t-dsp/t-dsp_core/3d_models/COMBO_XLR_NCJ6FI-H-0.stp

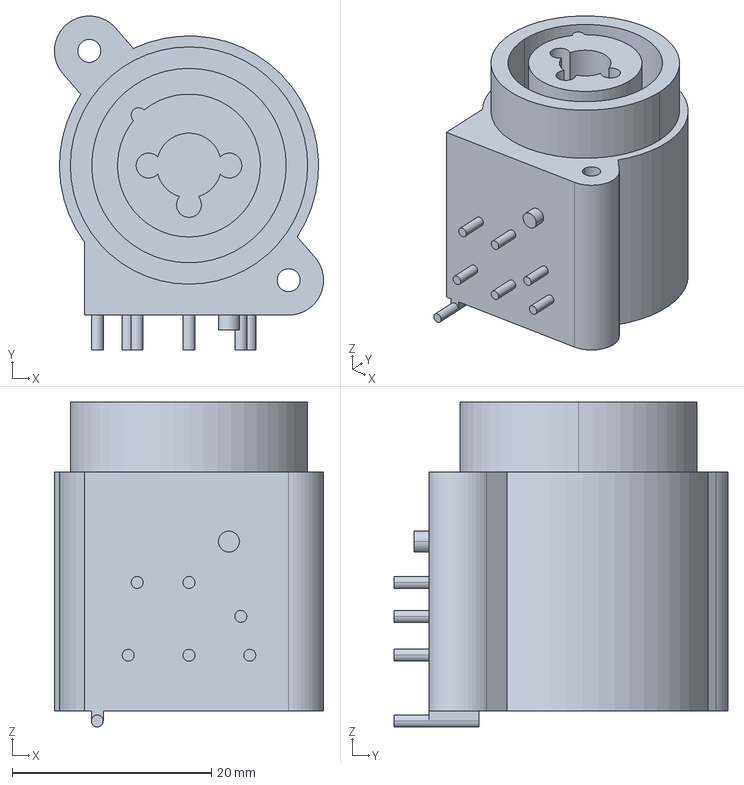
[picture p20: CAD file, 2026-02-28]
3d_models/COMBO_XLR_NCJ6FI-H-0.stp
27.0 x 33.5 x 32.6 mm
