t-dsp/t-dsp_core/3d_models/PRT-14417.step

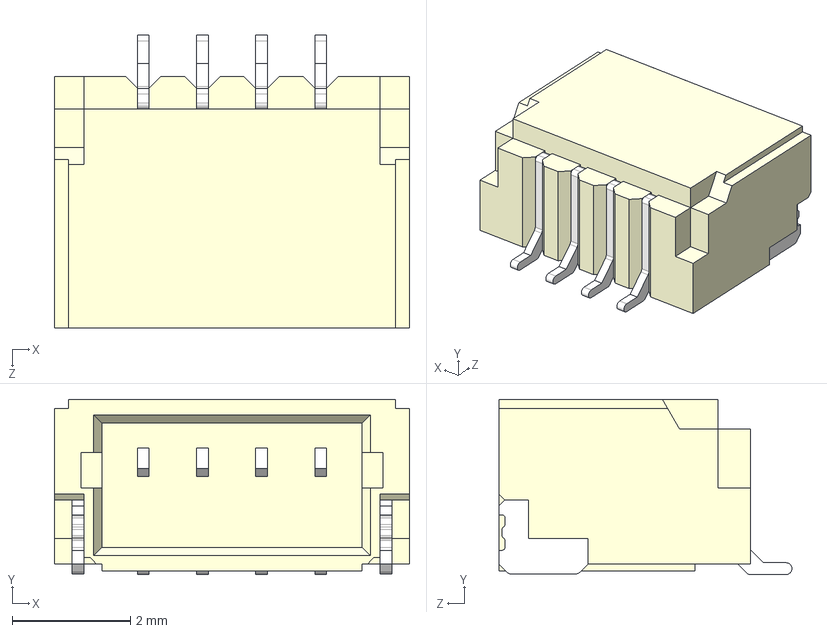
[picture p21: CAD file, 2026-02-28]
3d_models/PRT-14417.step
6.00 x 2.96 x 4.95 mm
