t-dsp/t-dsp_core/3d_models/COMBO-NCJ6FA-H.step

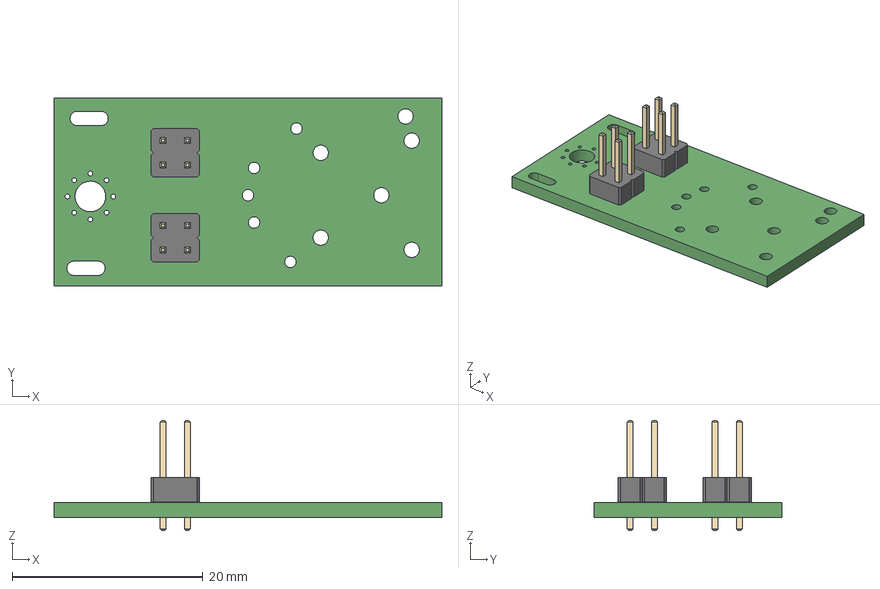
[picture p22: CAD file, 2026-02-28]
3d_models/COMBO-NCJ6FA-H.step
40.6 x 19.7 x 11.5 mm
