t-dsp/t-dsp_core/3d_models/35RAPC7JS_SIMPLIFIED.step

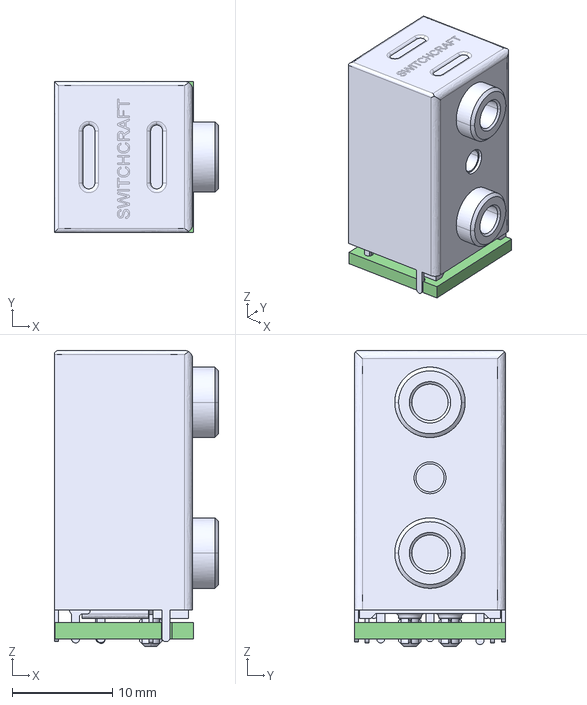
[picture p24: CAD file, 2026-02-28]
3d_models/35RAPC7JS_SIMPLIFIED.step
16.4 x 15.0 x 29.5 mm
IO_3.5_35RAPC7JS PCB
