t-dsp/t-dsp_core/3d_models/TFT_320x240_touch_r0.step

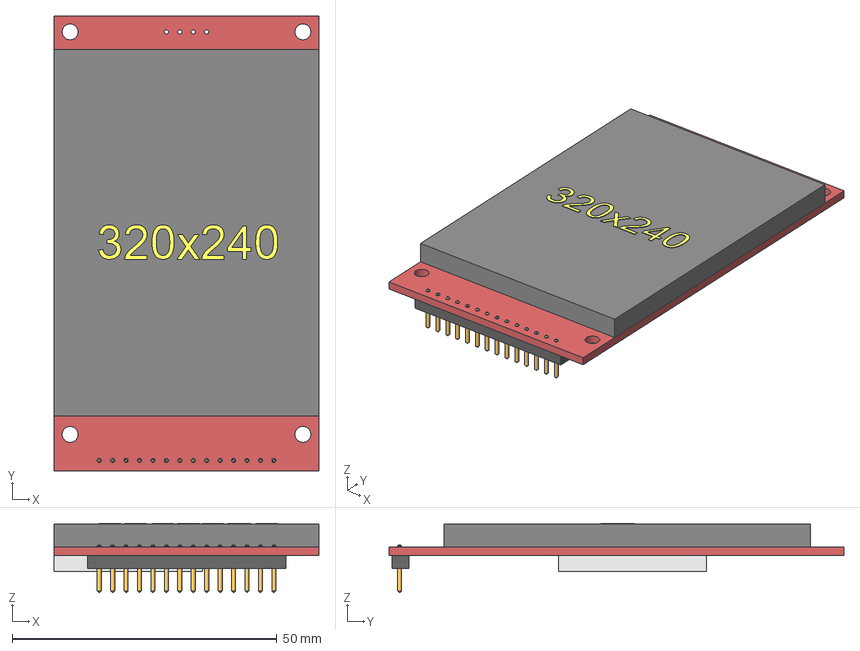
[picture p25: CAD file, 2026-02-28]
3d_models/TFT_320x240_touch_r0.step
50.0 x 86.0 x 13.1 mm
Body-header
Body-pins
Body-display
Body-sdcard
Body-board
