t-dsp/t-dsp_core/3d_models/pjras1x2s_Series.STEP

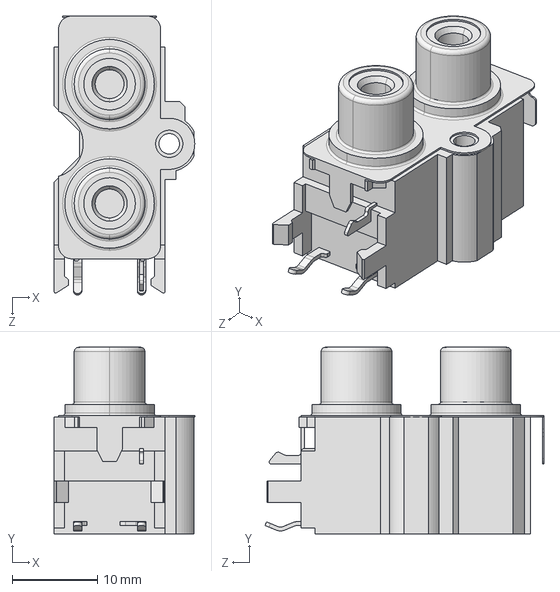
[picture p26: CAD file, 2026-02-28]
3d_models/pjras1x2s_Series.STEP
16.5 x 21.9 x 32.7 mm
