t-dsp/t-dsp_core/3d_models/MF-LSMF300_24X-2.stp

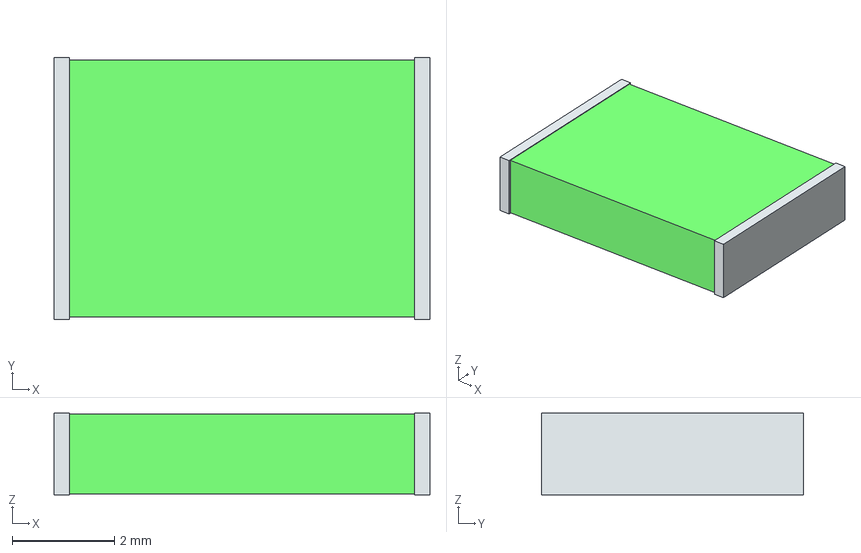
[picture p28: CAD file, 2026-02-28]
3d_models/MF-LSMF300_24X-2.stp
7.36 x 5.12 x 1.60 mm
term1
term2
