t-dsp/t-dsp_core/3d_models/EN11-HSM1AF15.STEP

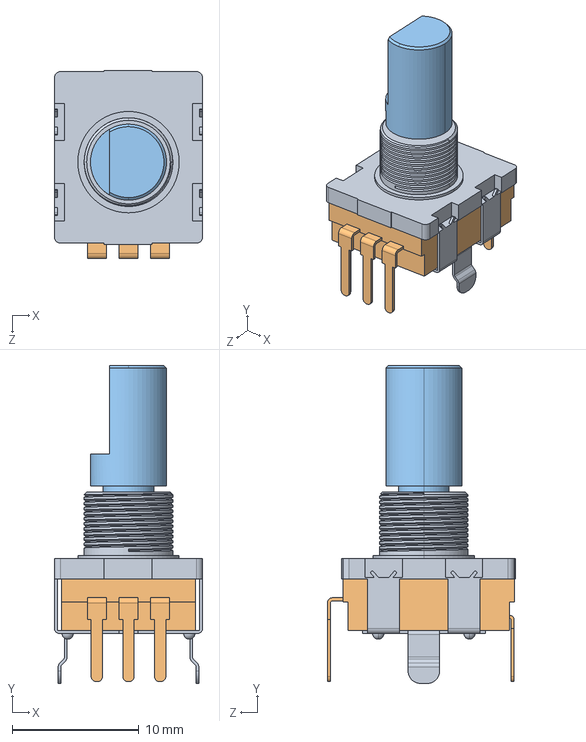
[picture p29: CAD file, 2026-02-28]
3d_models/EN11-HSM1AF15.STEP
11.7 x 25.1 x 14.9 mm
