t-dsp/t-dsp_core/3d_models/SD_CARD_DM3D-SF.step

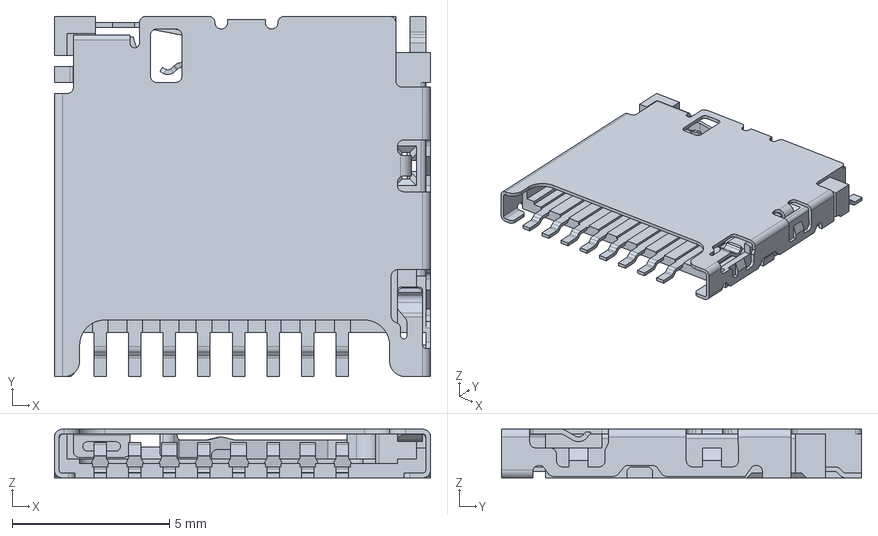
[picture p30: CAD file, 2026-02-28]
3d_models/SD_CARD_DM3D-SF.step
11.9 x 11.4 x 1.55 mm
