t-dsp/t-dsp_core/3d_models/SK6812.step

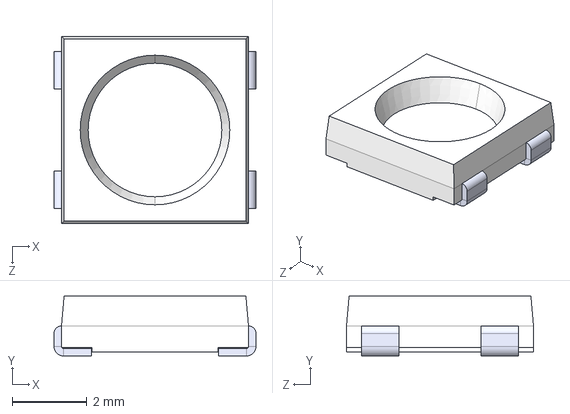
[picture p31: CAD file, 2026-02-28]
3d_models/SK6812.step
5.40 x 1.60 x 5.00 mm
