t-dsp/t-dsp_core/3d_models/c-292304-1-b-3d.stp

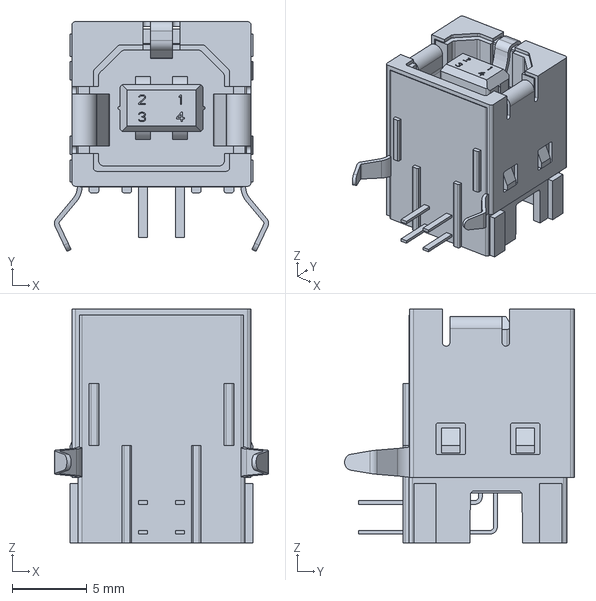
[picture p32: CAD file, 2026-02-28]
3d_models/c-292304-1-b-3d.stp
14.4 x 15.4 x 15.7 mm
