t-dsp/t-dsp_core/3d_models/PinHeader_2x02_P2.54mm_Vertical.step

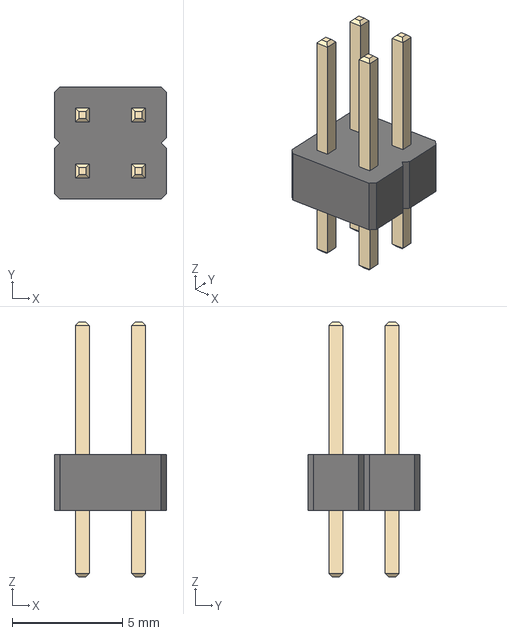
[picture p33: CAD file, 2026-02-28]
3d_models/PinHeader_2x02_P2.54mm_Vertical.step
5.08 x 5.08 x 11.5 mm
