t-dsp/t-dsp_core/3d_models/T10W--3DModel-STEP-56544.STEP

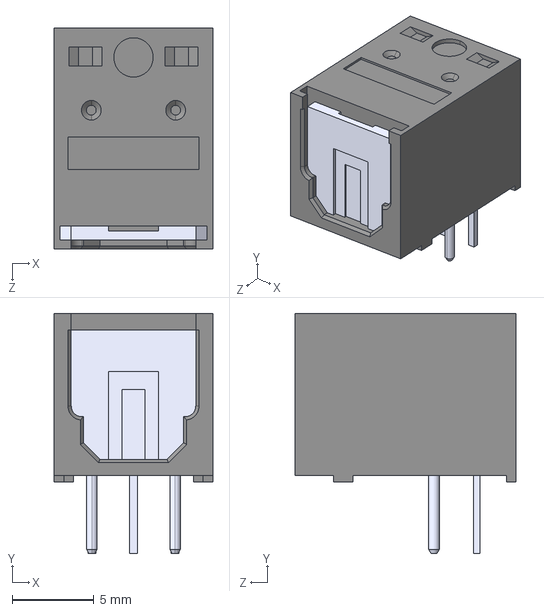
[picture p34: CAD file, 2026-02-28]
3d_models/T10W--3DModel-STEP-56544.STEP
9.70 x 14.7 x 13.5 mm
