t-dsp/t-dsp_core/3d_models/DIN-5.STEP

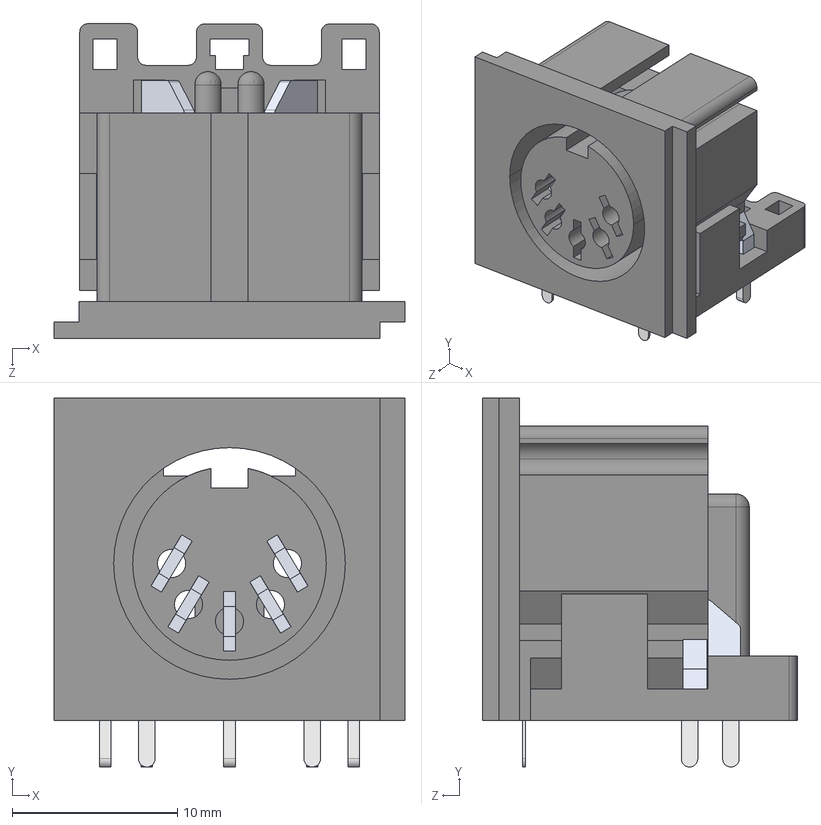
[picture p35: CAD file, 2026-02-28]
3d_models/DIN-5.STEP
21.2 x 22.3 x 19.0 mm
DIN5 A
DIN5 B
DIN5 C
DIN D x 2
DIN E x 2
DIN EE x 2
DIN G
DIN DD x 2
