t-dsp/t-dsp_core/3d_models/TOSLINK_3D_MODEL_PLT133_T9.step

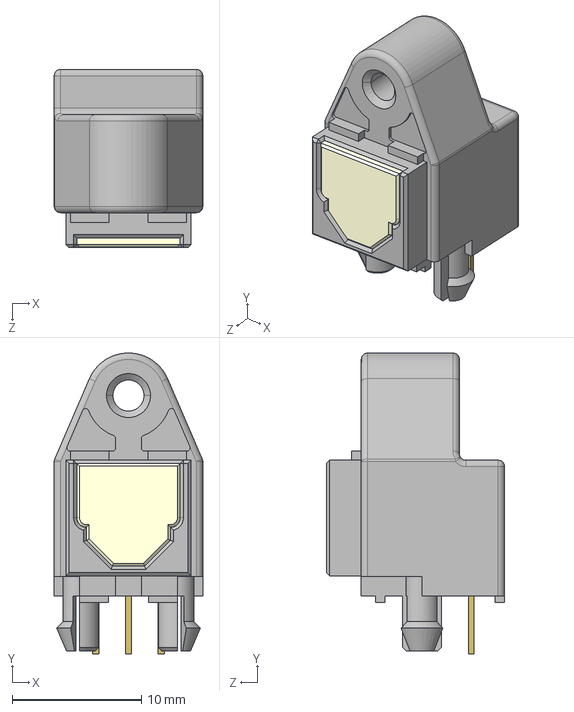
[picture p36: CAD file, 2026-02-28]
3d_models/TOSLINK_3D_MODEL_PLT133_T9.step
11.5 x 23.3 x 13.8 mm
