t-dsp/t-dsp_core/3d_models/Same_Sky_SJ3-35083D-TR.step

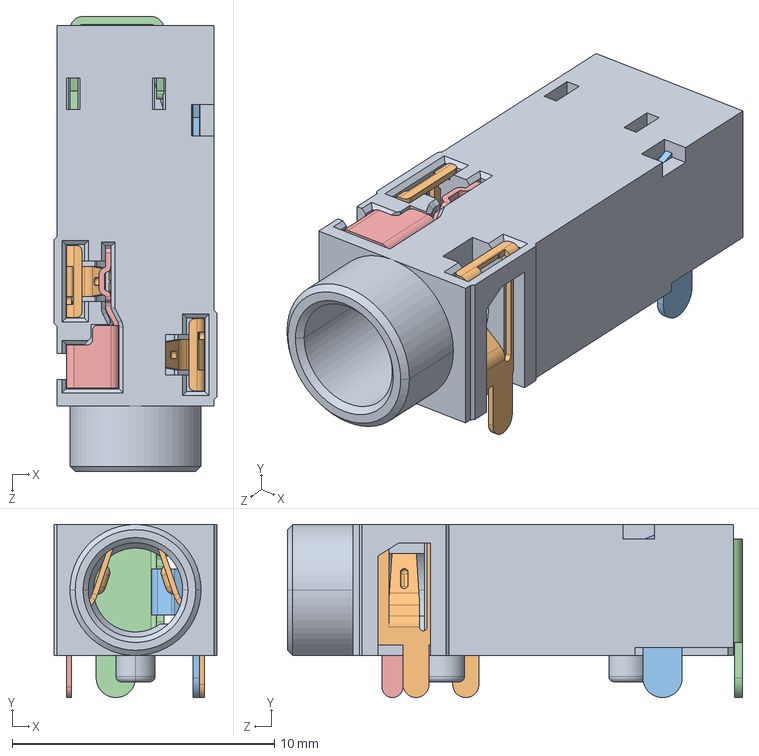
[picture p37: CAD file, 2026-02-28]
3d_models/Same_Sky_SJ3-35083D-TR.step
6.20 x 6.60 x 17.3 mm
