t-dsp/t-dsp_core/3d_models/2120--3DModel-STEP-630548.STEP

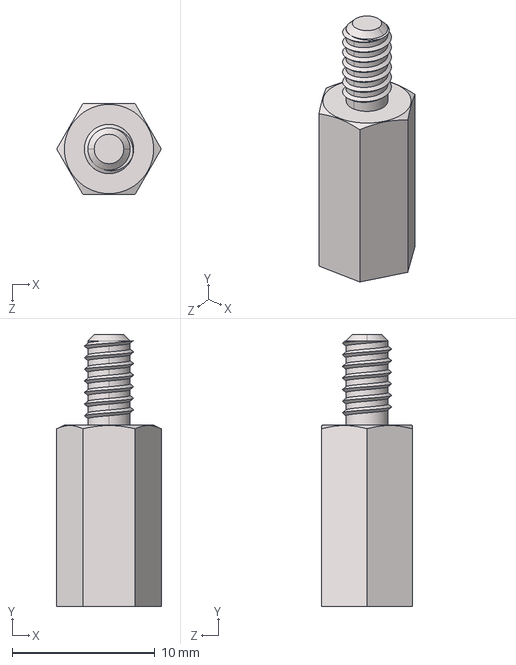
[picture p38: CAD file, 2026-02-28]
3d_models/2120--3DModel-STEP-630548.STEP
7.33 x 19.1 x 6.35 mm
