t-dsp/t-dsp_core/3d_models/3.5MM_STEREO_35RAPC4BHN2.STEP

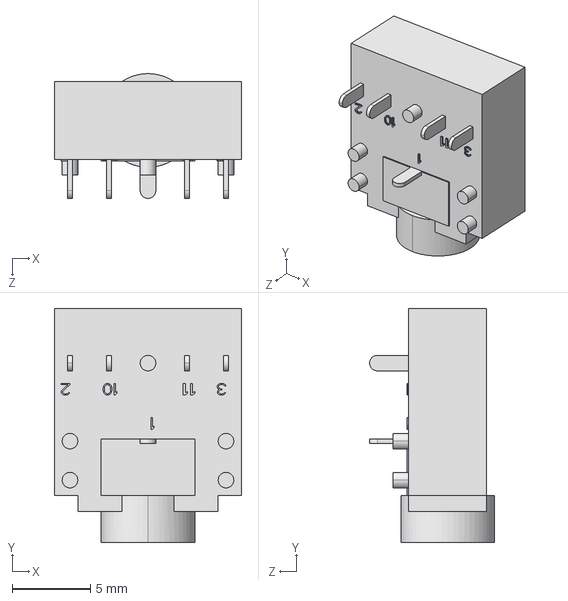
[picture p39: CAD file, 2026-02-28]
3d_models/3.5MM_STEREO_35RAPC4BHN2.STEP
12.0 x 15.0 x 8.00 mm
