t-dsp/t-dsp_core/3d_models/SPDIF_pjran1x1_Series.STEP

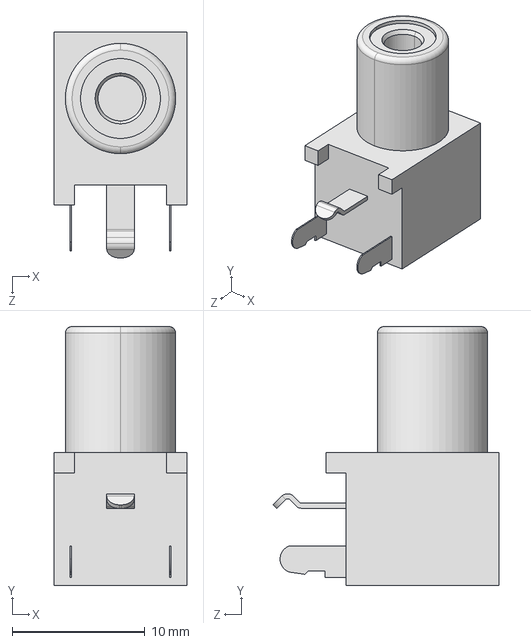
[picture p40: CAD file, 2026-02-28]
3d_models/SPDIF_pjran1x1_Series.STEP
10.00 x 19.5 x 17.0 mm
