t-dsp/t-dsp_core/3d_models/LED_SK6812MINI-E.step

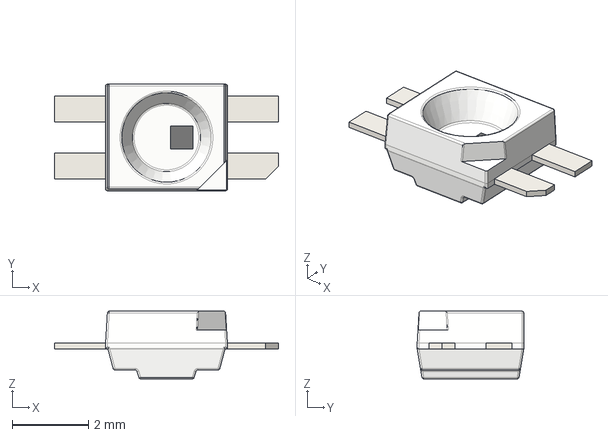
[picture p41: CAD file, 2026-02-28]
3d_models/LED_SK6812MINI-E.step
5.88 x 2.80 x 1.78 mm
