t-dsp/t-dsp_core/3d_models/USB-B1HS - USB-B1H Interconnect USB Type B.stp

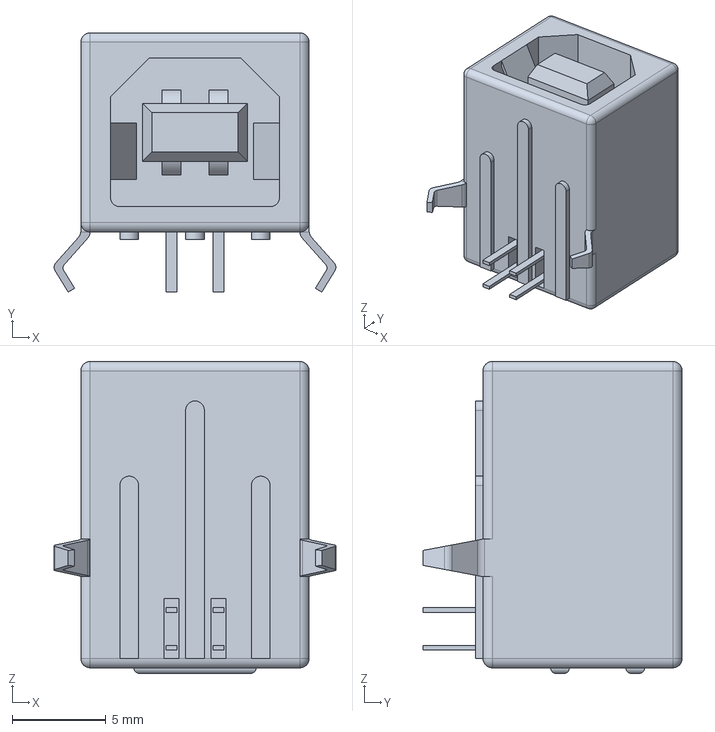
[picture p42: CAD file, 2026-02-28]
3d_models/USB-B1HS - USB-B1H Interconnect USB Type B.stp
15.0 x 13.8 x 16.6 mm
