t-dsp/t-dsp_core/3d_models/CP_Radial_D10.0mm_P5.00mm.step

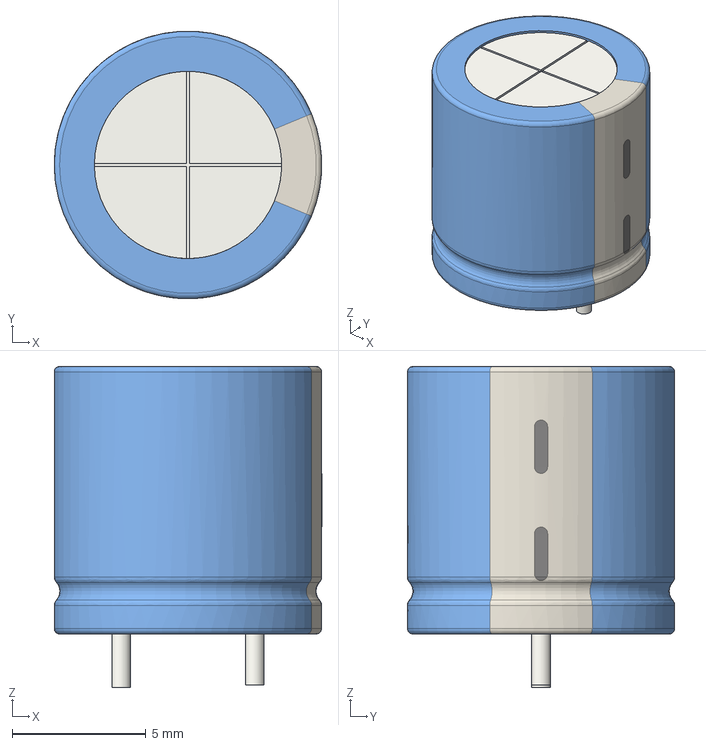
[picture p43: CAD file, 2026-02-28]
3d_models/CP_Radial_D10.0mm_P5.00mm.step
10.00 x 9.99 x 12.0 mm
