t-dsp/t-dsp_core/3d_models/DMG2307L-7.stp

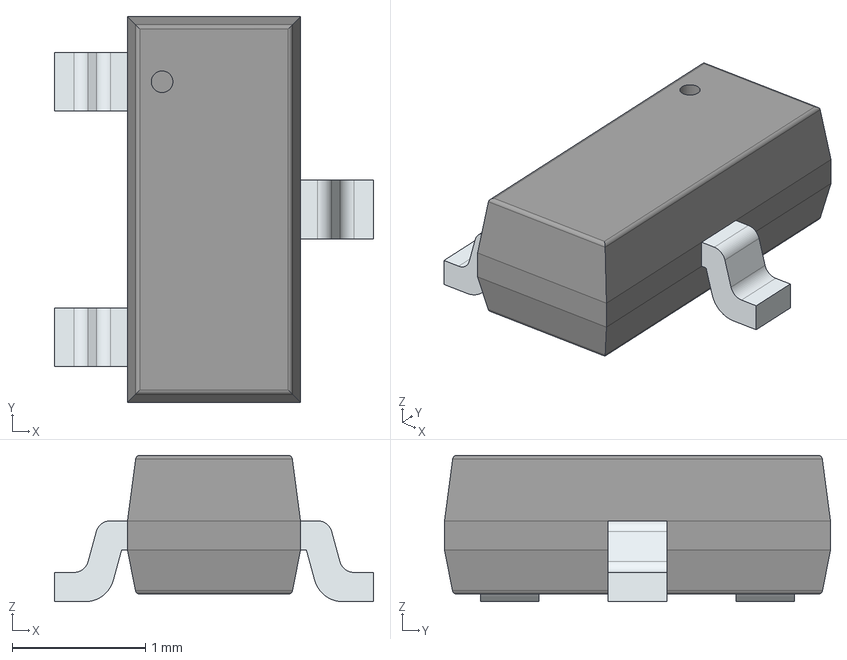
[picture p44: CAD file, 2026-02-28]
3d_models/DMG2307L-7.stp
2.40 x 2.90 x 1.10 mm
PinsArrayL
FilletPinR
