t-dsp/t-dsp_core/3d_models/SN74LVC1G66DBVR.stp

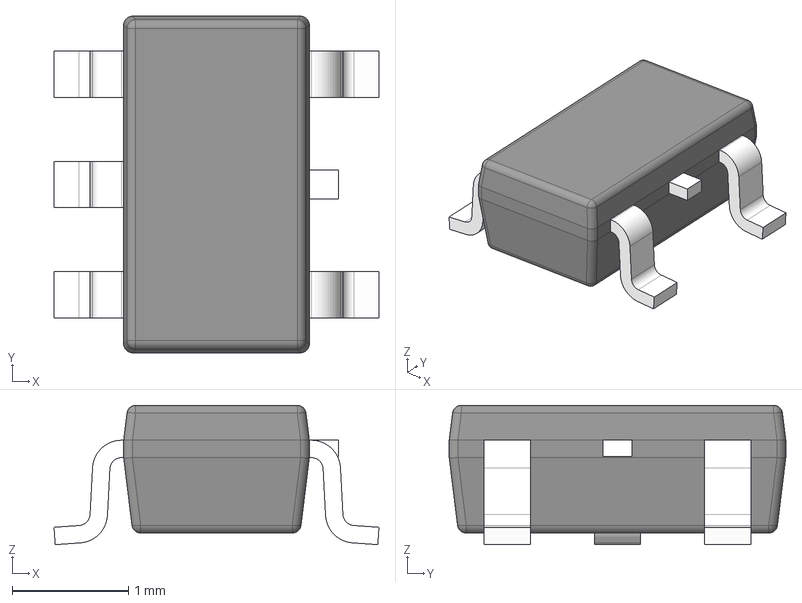
[picture p45: CAD file, 2026-02-28]
3d_models/SN74LVC1G66DBVR.stp
2.80 x 2.90 x 1.20 mm
BODY-SOT
LEAD-SOT x 5
LEAD-DUMMY
