t-dsp/t-dsp_core/3d_models/SOT-23-6.step

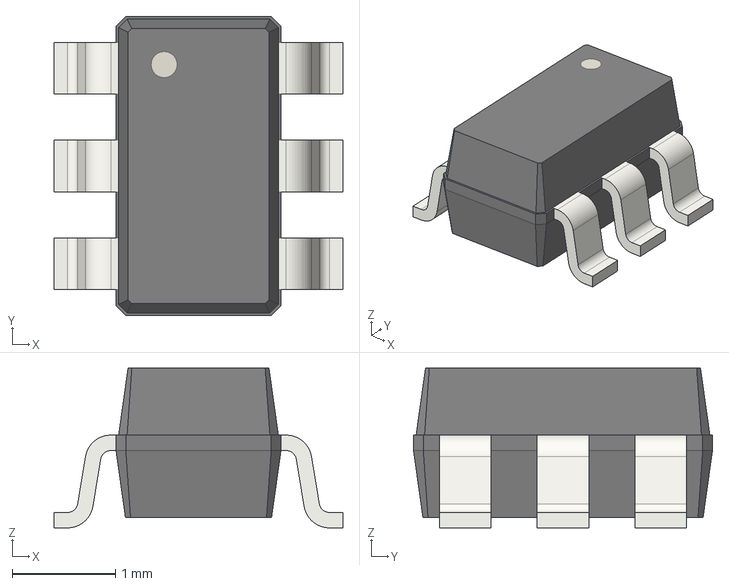
[picture p46: CAD file, 2026-02-28]
3d_models/SOT-23-6.step
2.80 x 2.90 x 1.55 mm
