t-dsp/t-dsp_core/3d_models/USB_A_c-292303-4-f-3d.stp

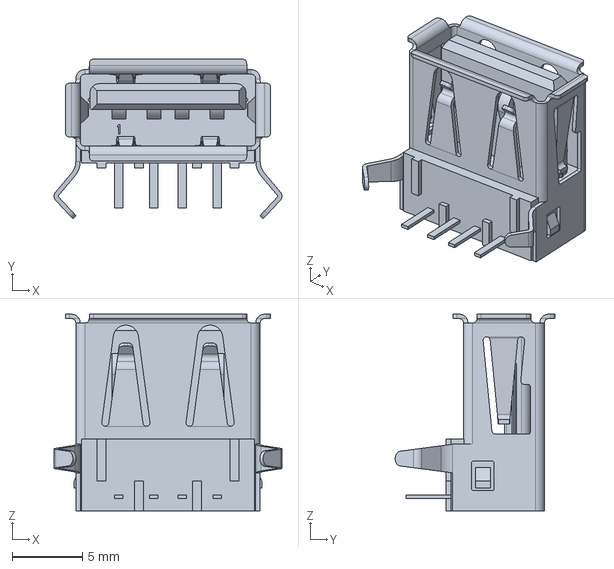
[picture p48: CAD file, 2026-02-28]
3d_models/USB_A_c-292303-4-f-3d.stp
16.2 x 11.4 x 14.0 mm
