t-dsp/t-dsp_core/3d_models/EC11E15204A3.stp

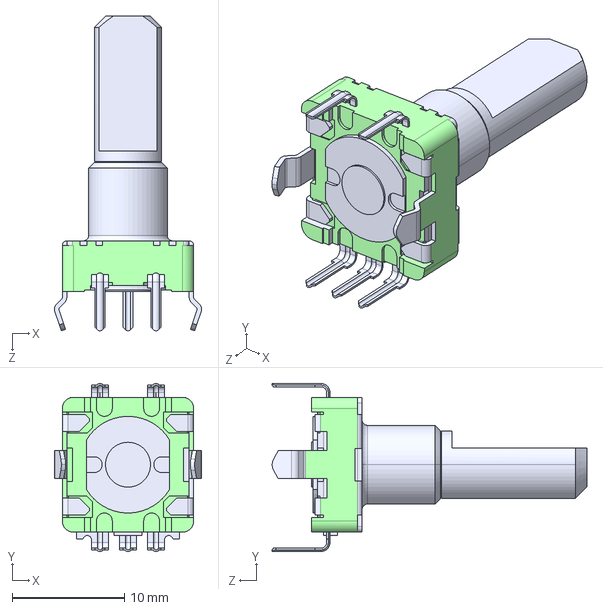
[picture p49: CAD file, 2026-02-28]
3d_models/EC11E15204A3.stp
13.1 x 14.9 x 28.0 mm
