t-dsp/t-dsp_core/3d_models/D_1210_3225Metric.step

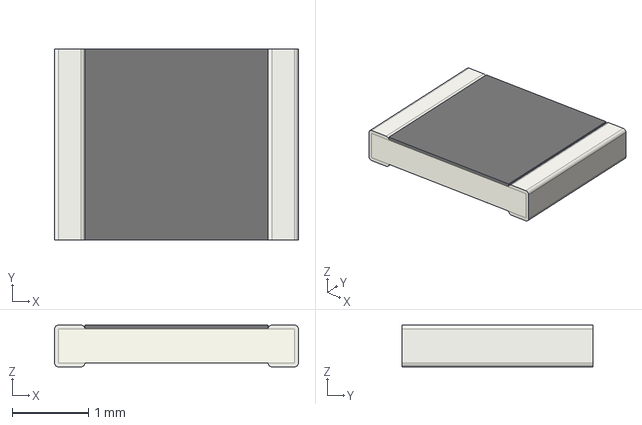
[picture p50: CAD file, 2026-02-28]
3d_models/D_1210_3225Metric.step
3.20 x 2.50 x 0.55 mm
