t-dsp/t-dsp_core/3d_models/IDC-Header_2x10_P2.54mm_Vertical.step

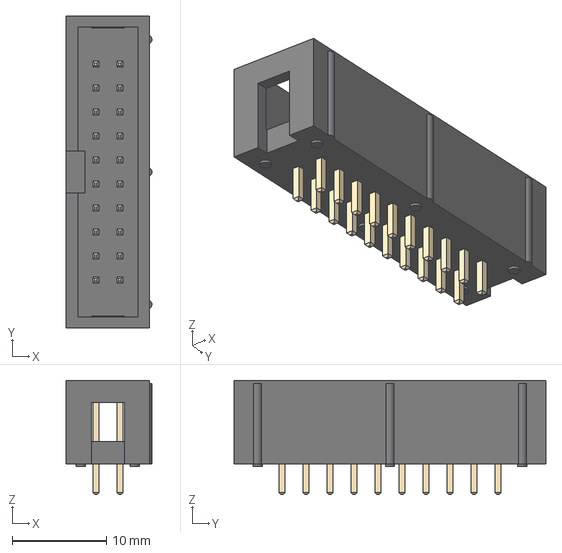
[picture p51: CAD file, 2026-02-28]
3d_models/IDC-Header_2x10_P2.54mm_Vertical.step
9.10 x 33.1 x 12.1 mm
