t-dsp/t-dsp_core/3d_models/PinHeader_2x04_P2.54mm_Vertical.step

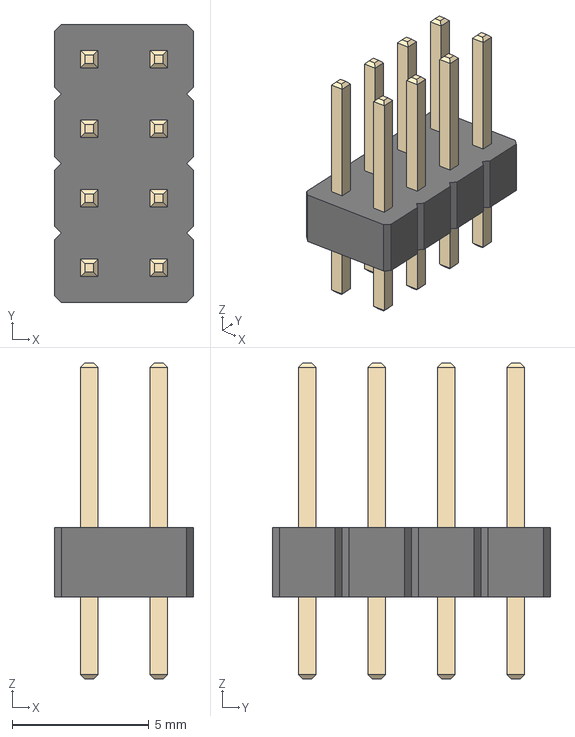
[picture p52: CAD file, 2026-02-28]
3d_models/PinHeader_2x04_P2.54mm_Vertical.step
5.08 x 10.2 x 11.5 mm
