t-dsp/t-dsp_core/3d_models/ncj6fav-1.stp

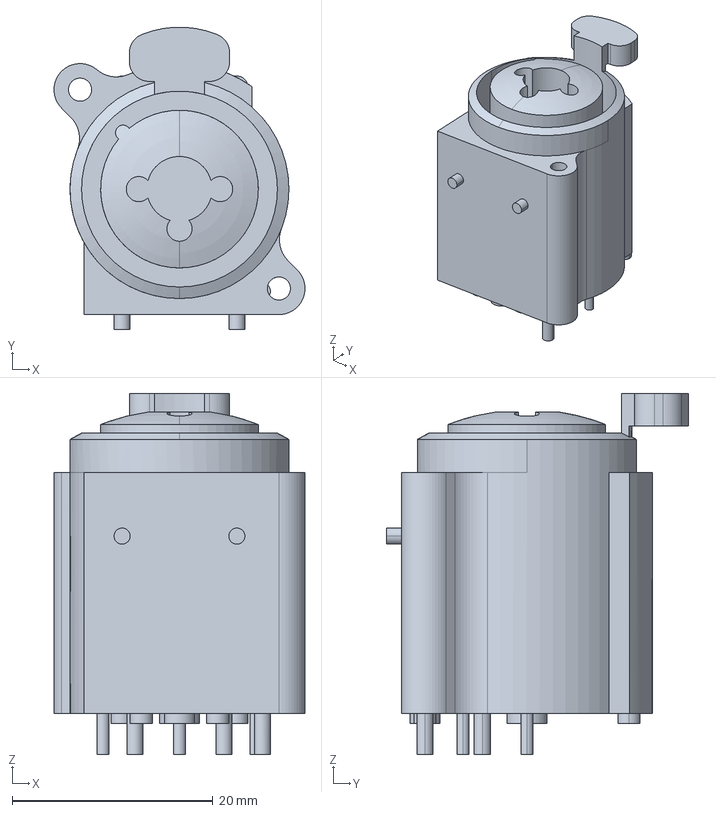
[picture p53: CAD file, 2026-02-28]
3d_models/ncj6fav-1.stp
25.0 x 30.1 x 36.0 mm
