t-dsp/t-dsp_core/3d_models/SOT-583-8.step

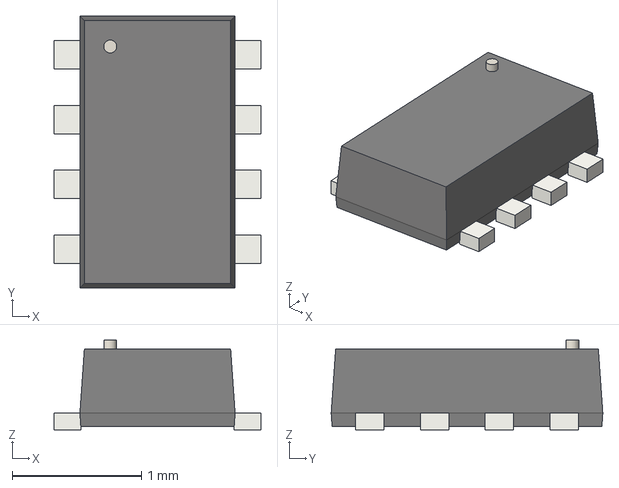
[picture p55: CAD file, 2026-02-28]
3d_models/SOT-583-8.step
1.60 x 2.10 x 0.695 mm
