t-dsp/t-dsp_core/3d_models/SN74LVC2G125DCTR.step

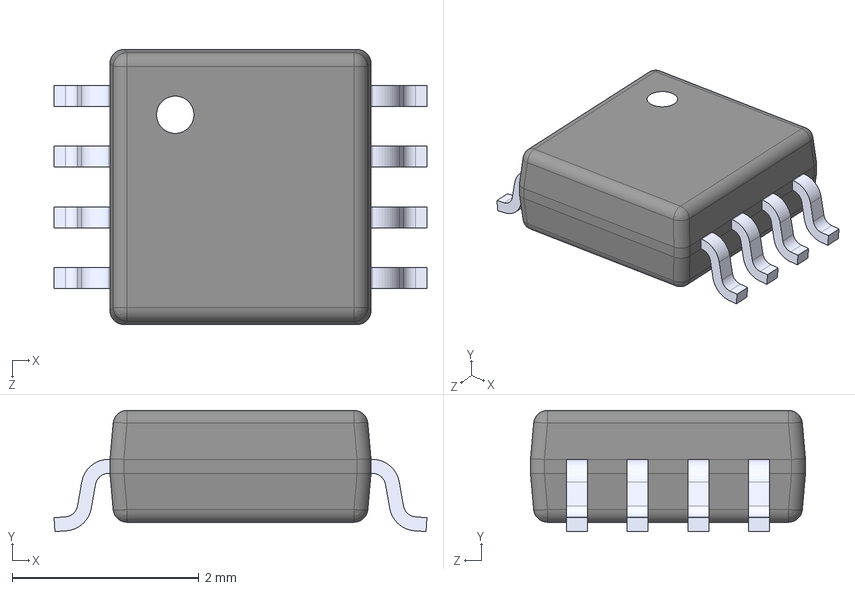
[picture p58: CAD file, 2026-02-28]
3d_models/SN74LVC2G125DCTR.step
4.00 x 1.30 x 2.95 mm
