t-dsp/t-dsp_core/3d_models/SOIC-14W_7.5x9.0mm_P1.27mm.step

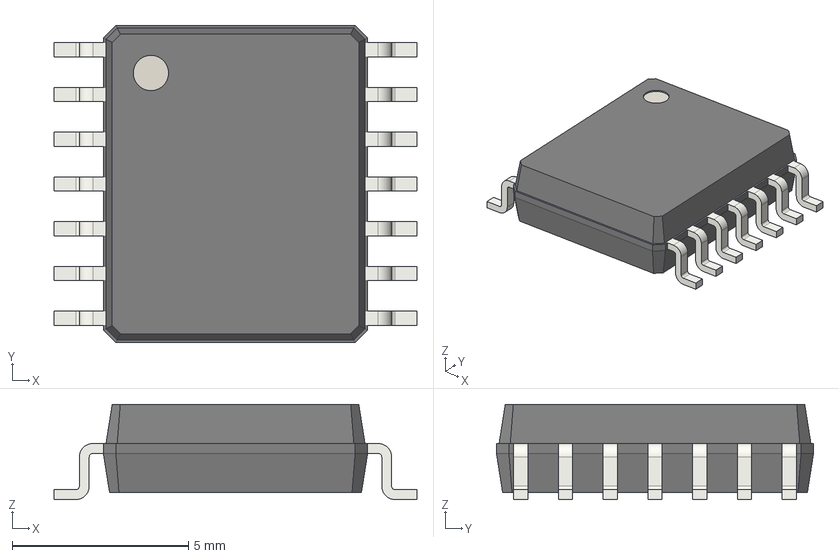
[picture p59: CAD file, 2026-02-28]
3d_models/SOIC-14W_7.5x9.0mm_P1.27mm.step
10.3 x 9.00 x 2.70 mm
