t-dsp/t-dsp_core/3d_models/JST_XH_S2B-XH-A_1x02_P2.50mm_Horizontal.step

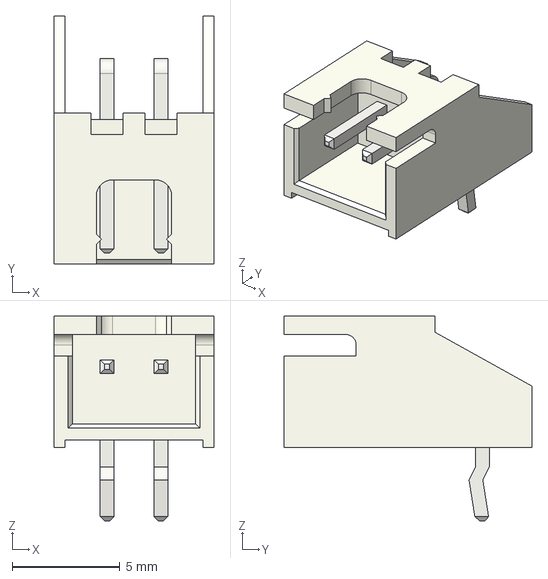
[picture p60: CAD file, 2026-02-28]
3d_models/JST_XH_S2B-XH-A_1x02_P2.50mm_Horizontal.step
7.40 x 11.5 x 9.50 mm
