t-dsp/t-dsp_core/3d_models/pjras2x2s_Series.STEP

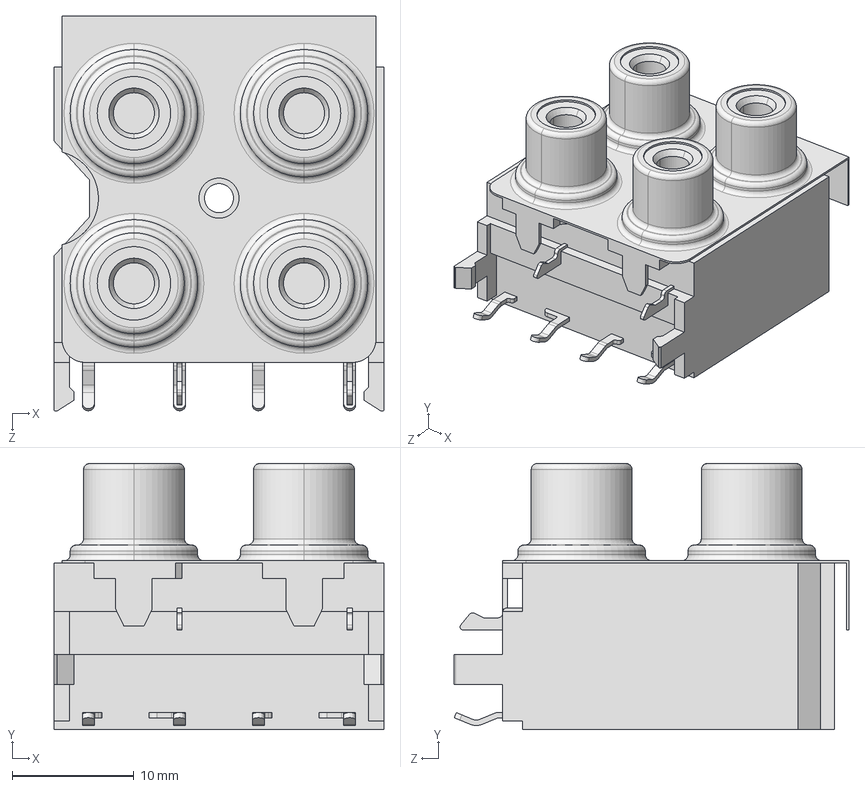
[picture p61: CAD file, 2026-02-28]
3d_models/pjras2x2s_Series.STEP
27.2 x 21.9 x 32.5 mm
