t-dsp/t-dsp_core/3d_models/C_1206_3216Metric.step

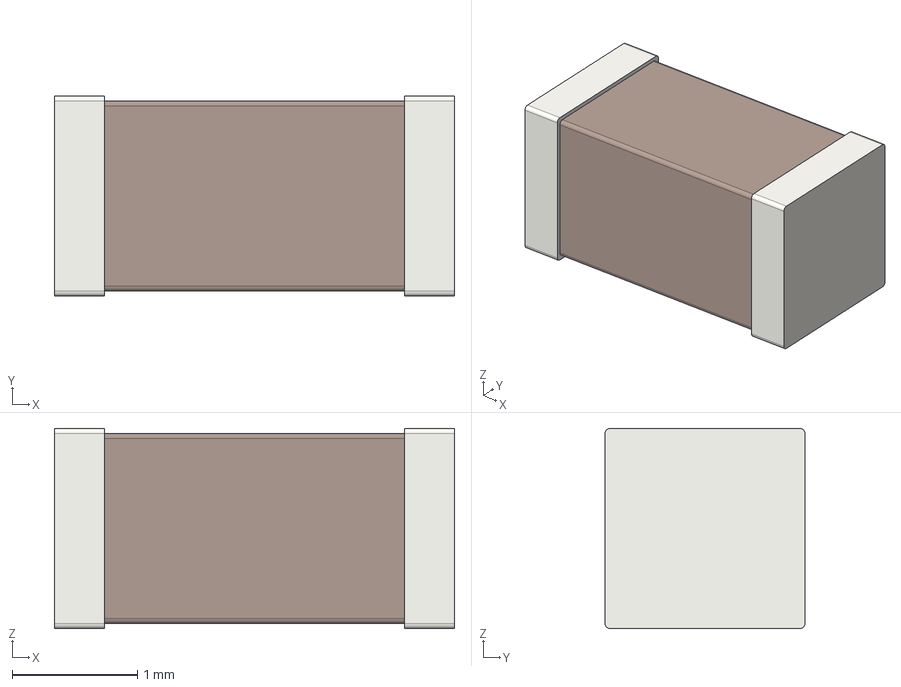
[picture p64: CAD file, 2026-02-28]
3d_models/C_1206_3216Metric.step
3.20 x 1.60 x 1.60 mm
