t-dsp/t-dsp_core/3d_models/PinSocket_1x08_P2.54mm_Vertical.step

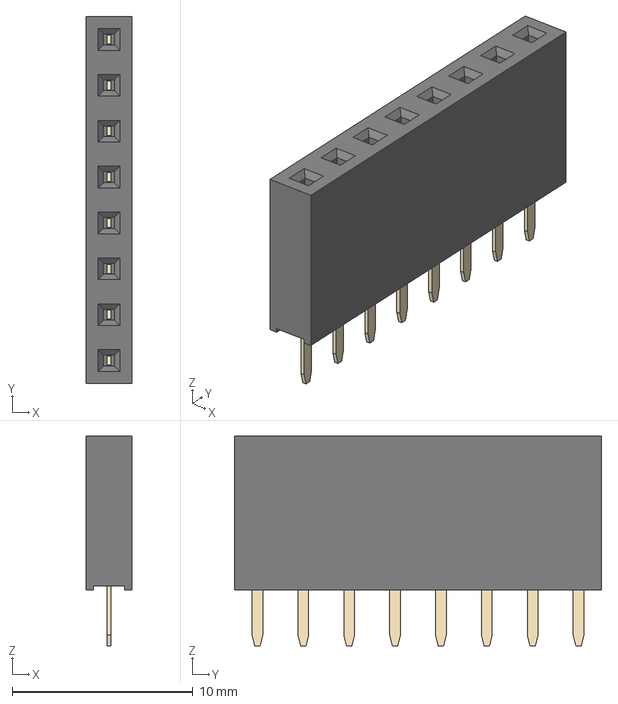
[picture p65: CAD file, 2026-02-28]
3d_models/PinSocket_1x08_P2.54mm_Vertical.step
2.54 x 20.3 x 11.6 mm
