t-dsp/t-dsp_core/3d_models/PEC12R-2220F-S0024.step

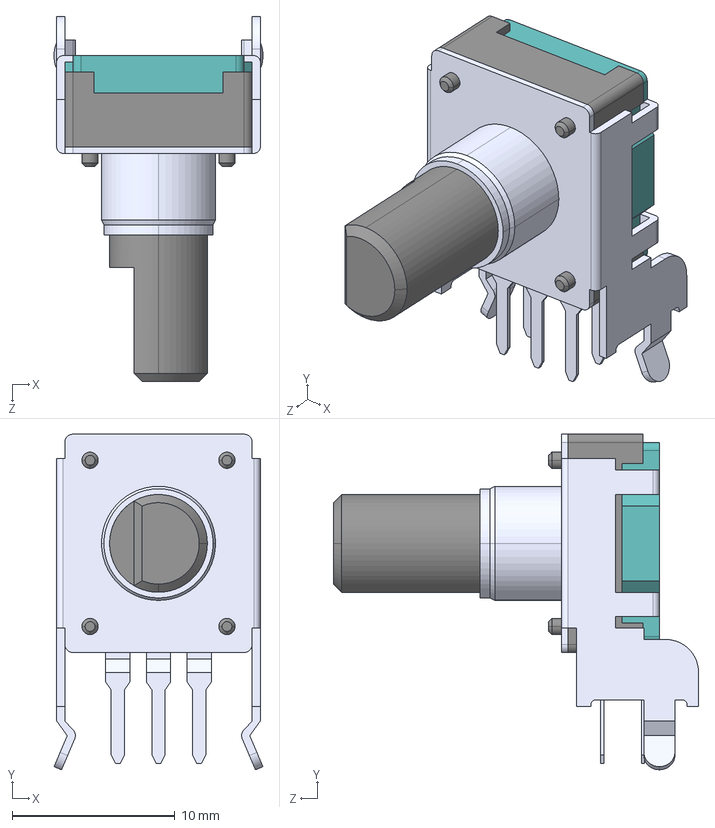
[picture p66: CAD file, 2026-02-28]
3d_models/PEC12R-2220F-S0024.step
12.8 x 20.6 x 22.4 mm
