t-dsp/t-dsp_core/3d_models/DC_BARREL_PJ-202AH.step

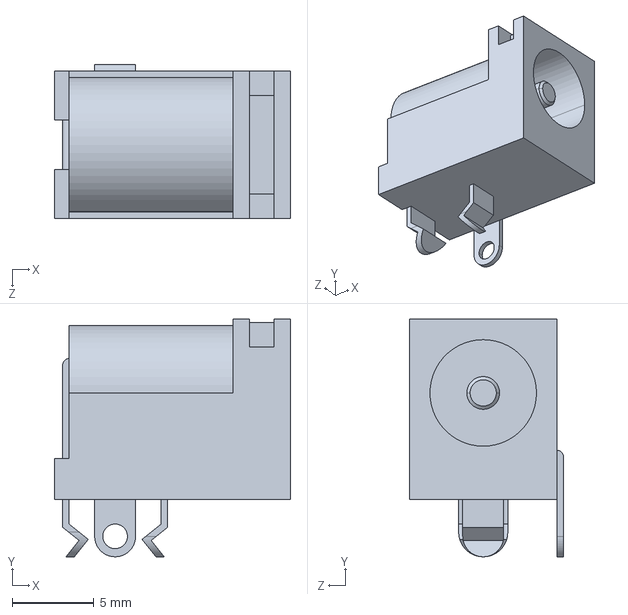
[picture p68: CAD file, 2026-02-28]
3d_models/DC_BARREL_PJ-202AH.step
14.4 x 14.5 x 9.40 mm
