t-dsp/t-dsp_core/3d_models/J1B1211CCD.STEP

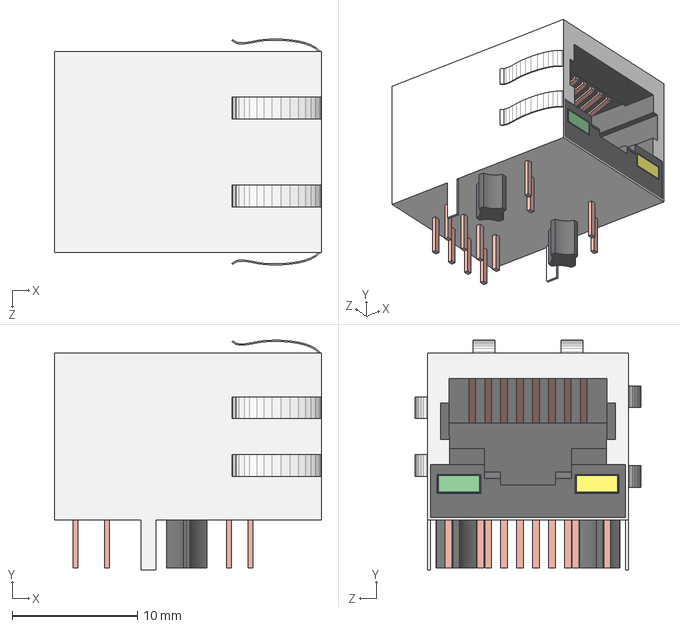
[picture p69: CAD file, 2026-02-28]
3d_models/J1B1211CCD.STEP
21.3 x 18.3 x 18.0 mm
