t-dsp/t-dsp_core/3d_models/TPD4E02B04DQA.step

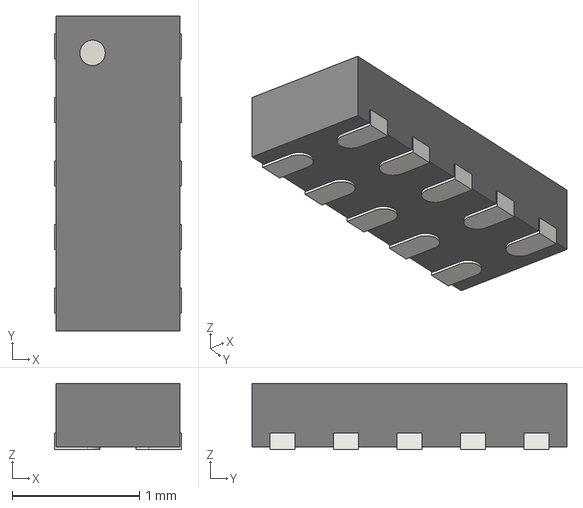
[picture p70: CAD file, 2026-02-28]
3d_models/TPD4E02B04DQA.step
1.00 x 2.48 x 0.52 mm
