t-dsp/t-dsp_core/3d_models/74HCT2G125DC,125.stp

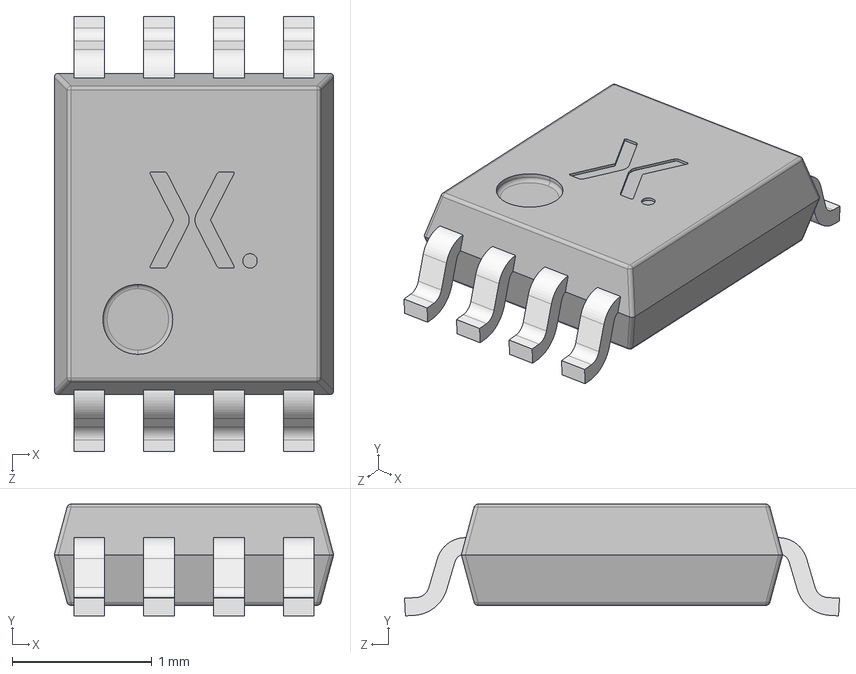
[picture p71: CAD file, 2026-02-28]
3d_models/74HCT2G125DC,125.stp
2.00 x 0.8 x 3.11 mm
SOT765 Mold body
SOT765 Lead x 8
