t-dsp/t-dsp_core/3d_models/35RAPC3BH3.STEP

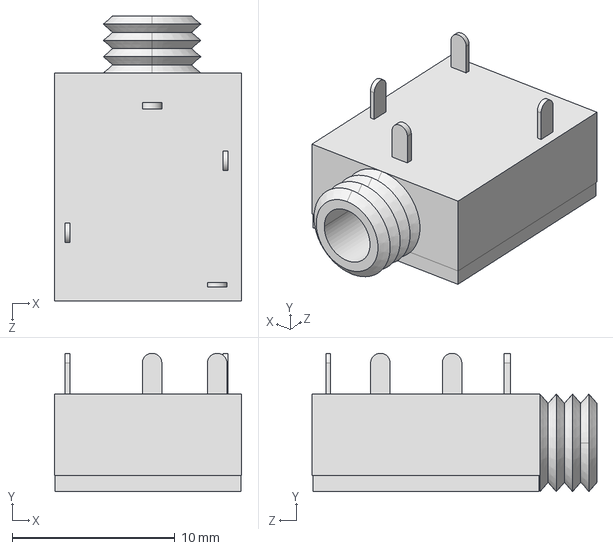
[picture p72: CAD file, 2026-02-28]
3d_models/35RAPC3BH3.STEP
11.5 x 8.50 x 17.5 mm
