t-dsp/t-dsp_core/3d_models/PinSocket_2x10_P2.54mm_Vertical.step

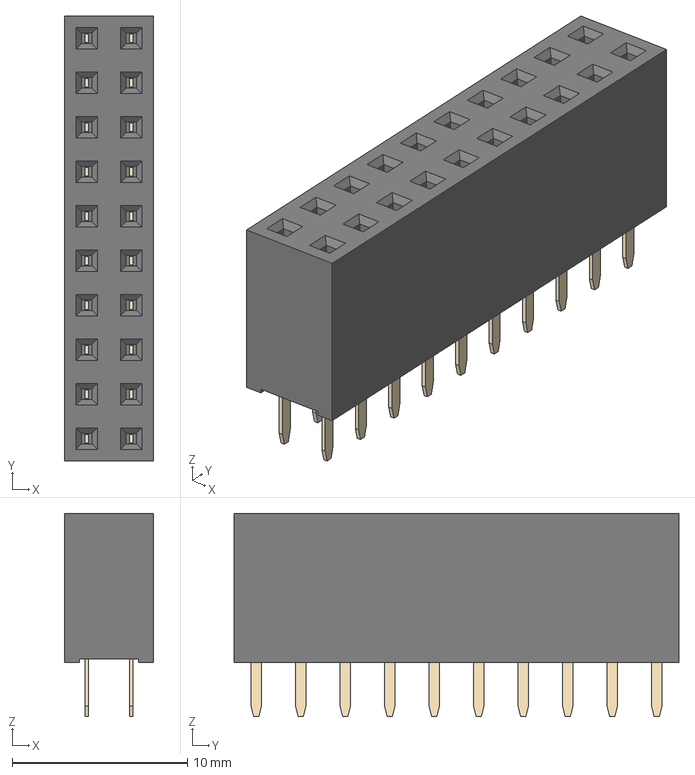
[picture p73: CAD file, 2026-02-28]
3d_models/PinSocket_2x10_P2.54mm_Vertical.step
5.08 x 25.4 x 11.6 mm
