t-dsp/t-dsp_core/3d_models/TPS2116DRLR.stp

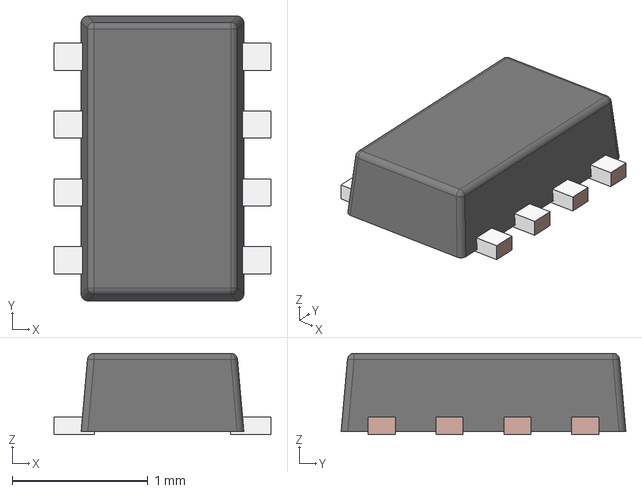
[picture p74: CAD file, 2026-02-28]
3d_models/TPS2116DRLR.stp
1.60 x 2.10 x 0.6 mm
FRAME-DRL0008A
BODY-SOT
