t-dsp/t-dsp_core/3d_models/JST - XH - Thru (V) - 2Pin - 2.54mm.stp

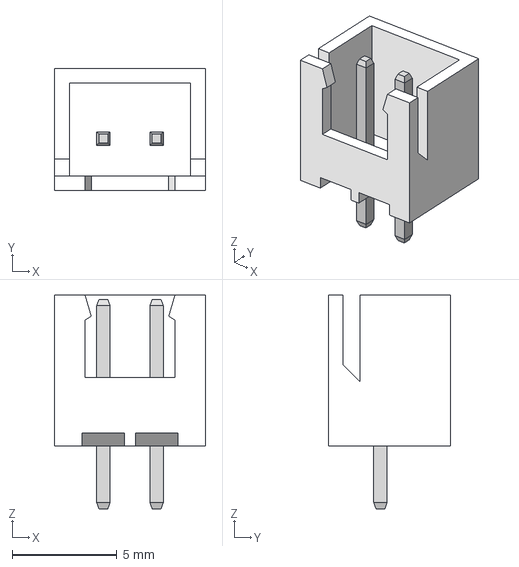
[picture p75: CAD file, 2026-02-28]
3d_models/JST - XH - Thru (V) - 2Pin - 2.54mm.stp
7.21 x 5.84 x 10.2 mm
