t-dsp/t-dsp_core/3d_models/1808--3DModel-STEP-630548.STEP

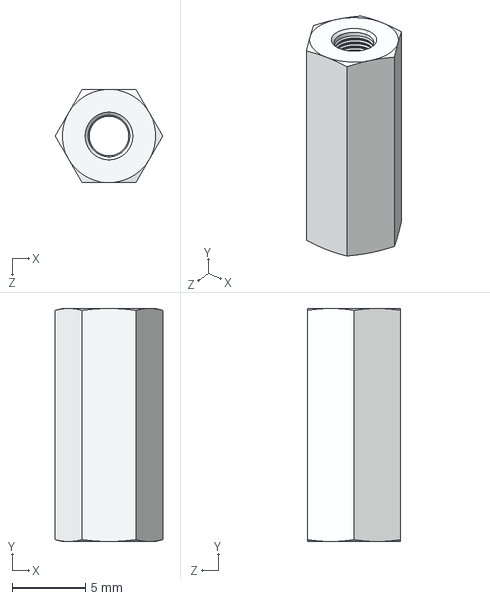
[picture p76: CAD file, 2026-02-28]
3d_models/1808--3DModel-STEP-630548.STEP
7.33 x 15.9 x 6.35 mm
