t-dsp/t-dsp_core/3d_models/TPD1E10B06DPYT.stp

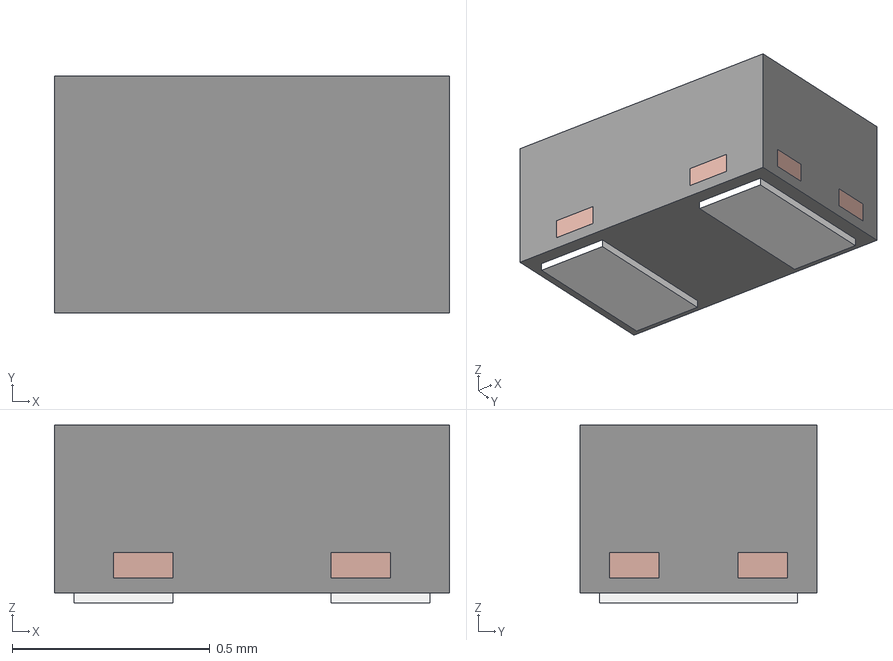
[picture p77: CAD file, 2026-02-28]
3d_models/TPD1E10B06DPYT.stp
1.00 x 0.6 x 0.45 mm
BODY-SON
FRAME-DPY0002A
