t-dsp/t-dsp_core/3d_models/3-D NCJ6FAH.stp

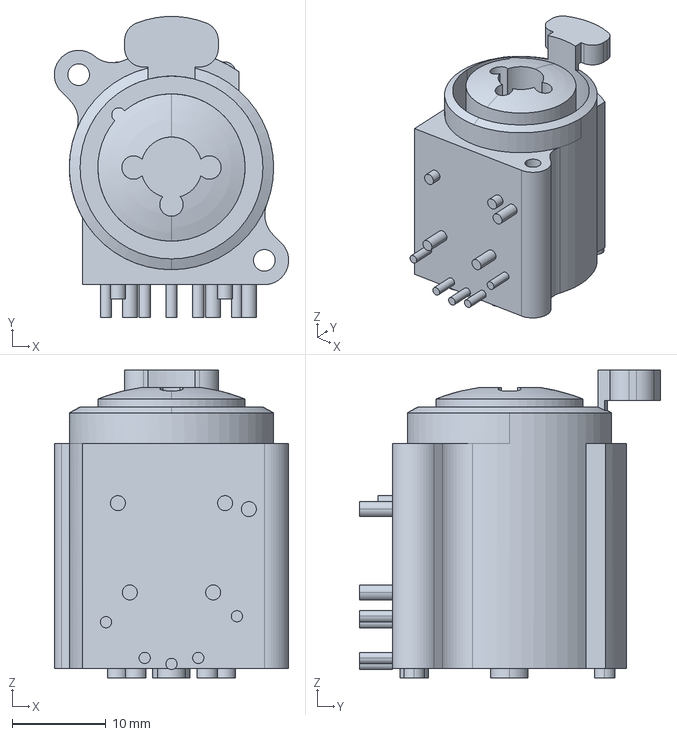
[picture p78: CAD file, 2026-02-28]
3d_models/3-D NCJ6FAH.stp
25.0 x 32.1 x 32.9 mm
