t-dsp/t-dsp_core/3d_models/PinSocket_1x02_P2.54mm_Vertical.step

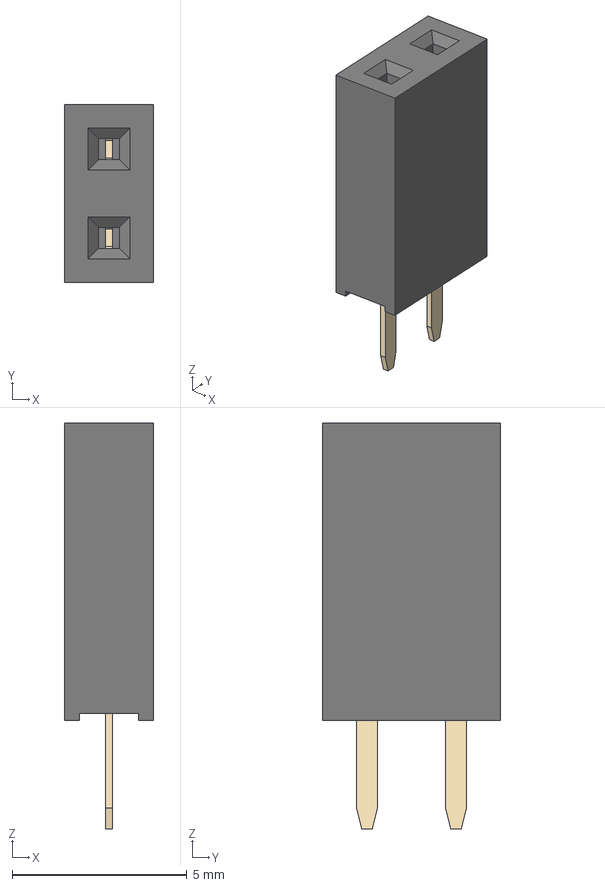
[picture p79: CAD file, 2026-02-28]
3d_models/PinSocket_1x02_P2.54mm_Vertical.step
2.54 x 5.08 x 11.6 mm
