t-dsp/t-dsp_core/3d_models/Tactile_Switch_4.54.5MM.stp

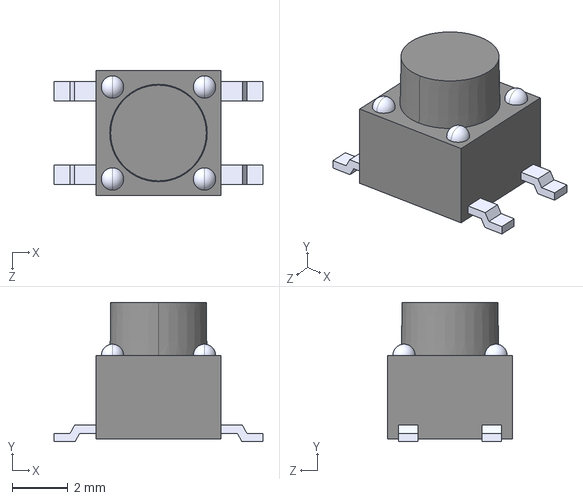
[picture p80: CAD file, 2026-02-28]
3d_models/Tactile_Switch_4.54.5MM.stp
7.50 x 5.00 x 4.50 mm
