t-dsp/t-dsp_core/3d_models/PJRAS2X1S01X.step

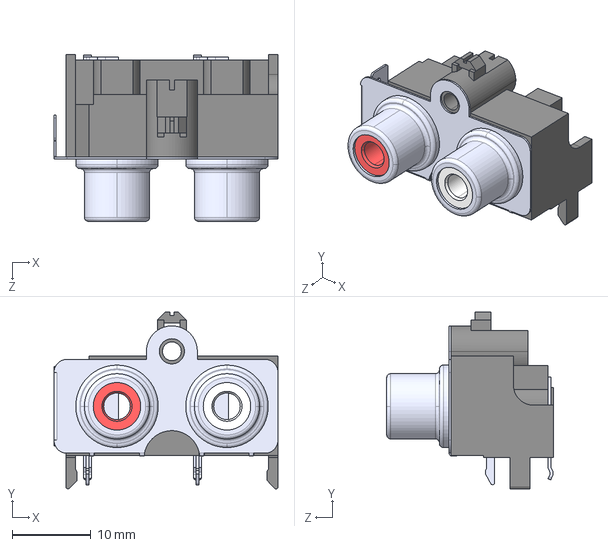
[picture p81: CAD file, 2026-02-28]
3d_models/PJRAS2X1S01X.step
28.5 x 22.5 x 21.2 mm
