t-dsp/t-dsp_core/3d_models/35RAPC7JS.STEP

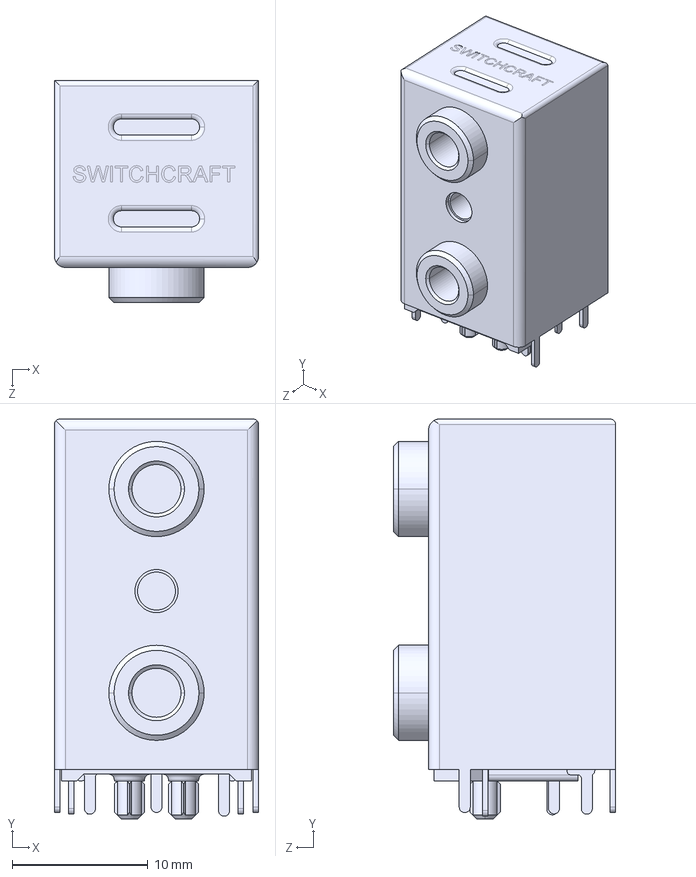
[picture p82: CAD file, 2026-02-28]
3d_models/35RAPC7JS.STEP
15.0 x 29.5 x 16.4 mm
