t-dsp/t-dsp_core/3d_models/PinHeader_1x09_P2.54mm_Vertical.step

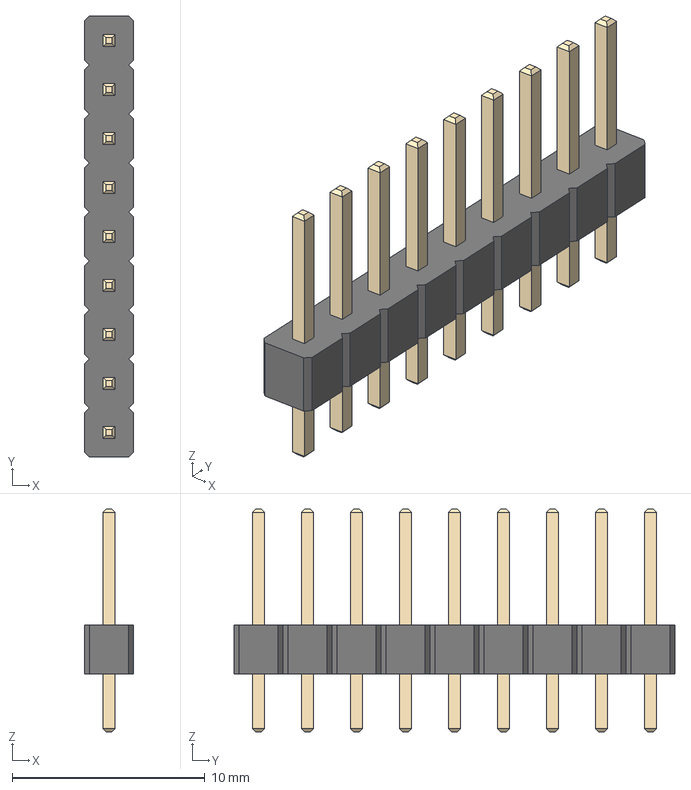
[picture p84: CAD file, 2026-02-28]
3d_models/PinHeader_1x09_P2.54mm_Vertical.step
2.54 x 22.9 x 11.5 mm
