t-dsp/t-dsp_core/3d_models/Same_Sky_SJ3-35044A.step

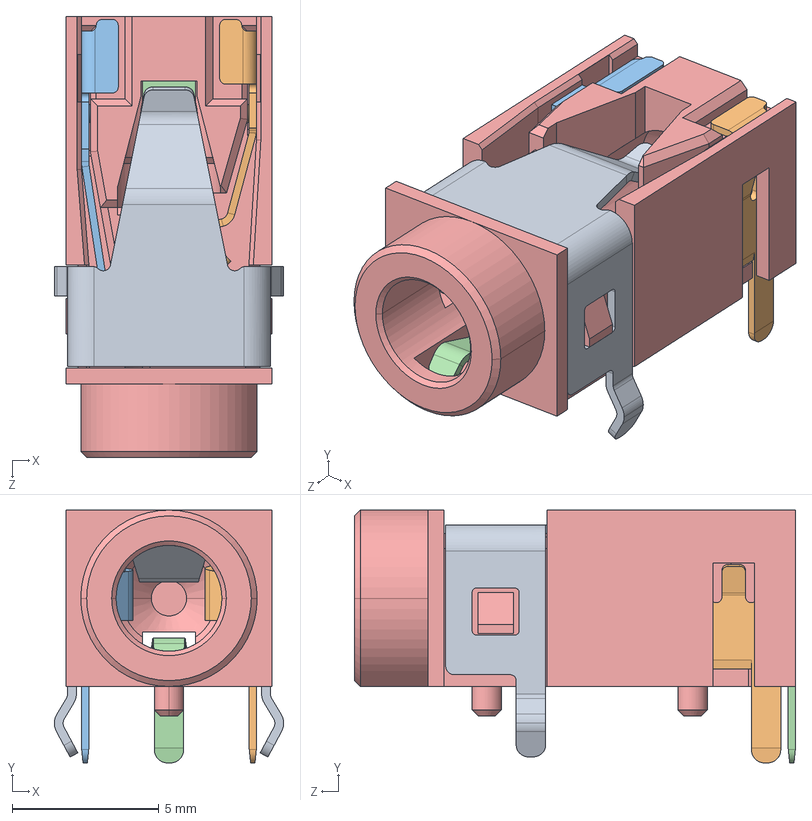
[picture p85: CAD file, 2026-02-28]
3d_models/Same_Sky_SJ3-35044A.step
7.80 x 8.60 x 15.0 mm
