t-dsp/t-dsp_core/3d_models/PinHeader_1x08_P2.54mm_Vertical.step

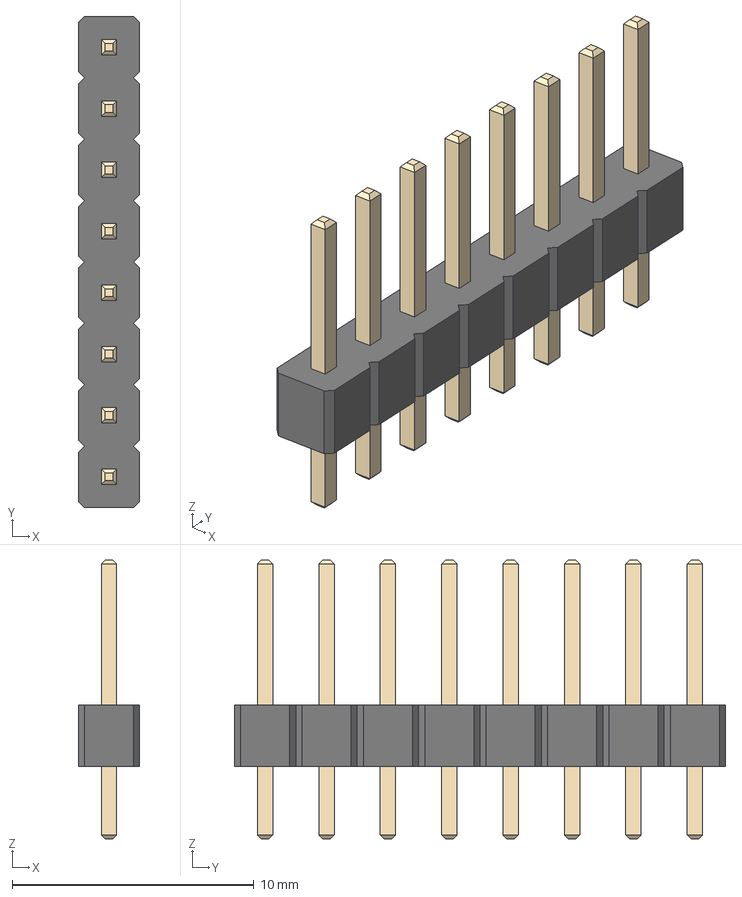
[picture p86: CAD file, 2026-02-28]
3d_models/PinHeader_1x08_P2.54mm_Vertical.step
2.54 x 20.3 x 11.5 mm
