t-dsp/t-dsp_core/3d_models/3-d-nmj6hcd3.stp

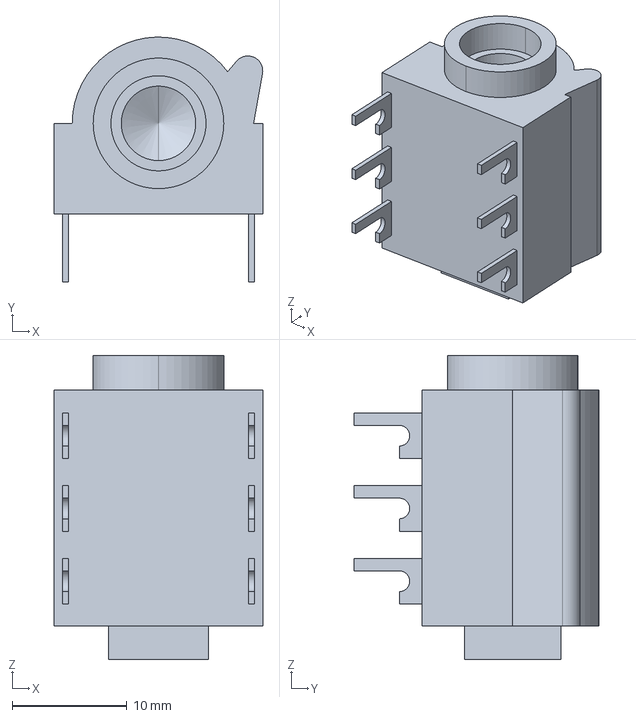
[picture p89: CAD file, 2026-02-28]
3d_models/3-d-nmj6hcd3.stp
18.2 x 21.4 x 26.5 mm
