t-dsp/t-dsp_core/3d_models/4691.step

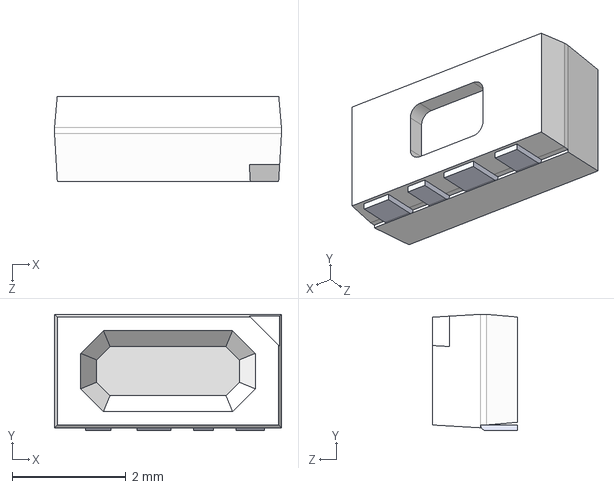
[picture p90: CAD file, 2026-02-28]
3d_models/4691.step
4.00 x 2.05 x 1.50 mm
