t-dsp/t-dsp_core/3d_models/TE_1775485-1_BATTERY.step

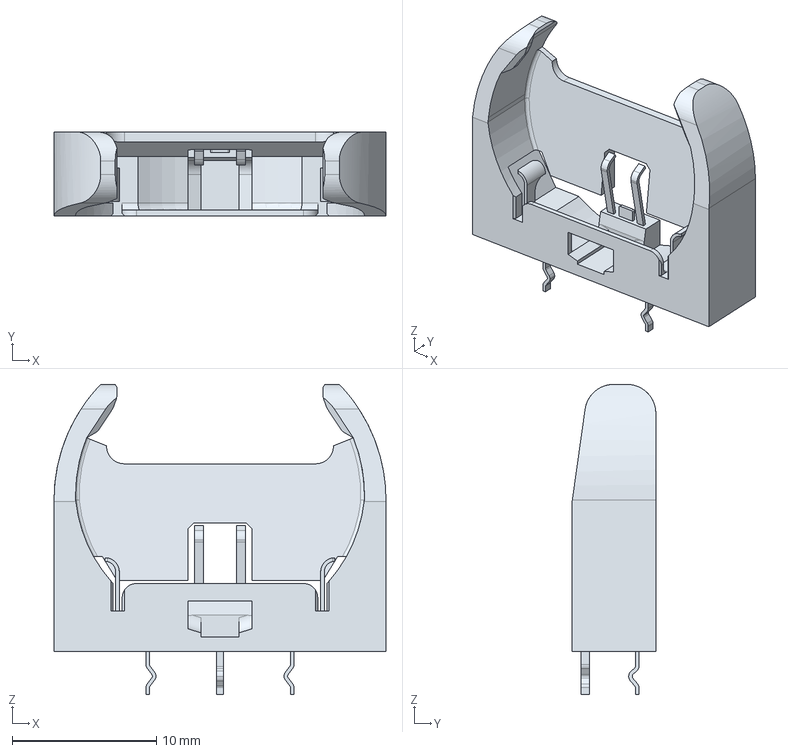
[picture p91: CAD file, 2026-02-28]
3d_models/TE_1775485-1_BATTERY.step
23.0 x 5.80 x 21.5 mm
